Funky-Circuit/MOD1Bass/MOD1Bass_models/esp_lid.stl

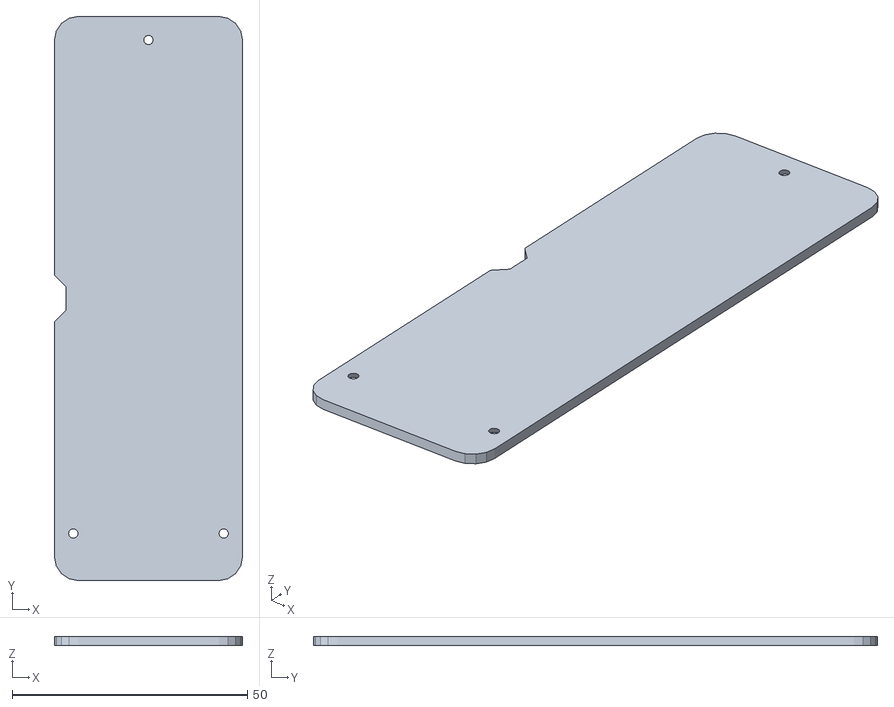
[picture p15: CAD file, 2026-07-26]
MOD1Bass_models/esp_lid.stl
40.0 x 120.0 x 2.00
