Funky-Circuit/MOD1Bass/MOD1Bass_models/body_right_b.stl

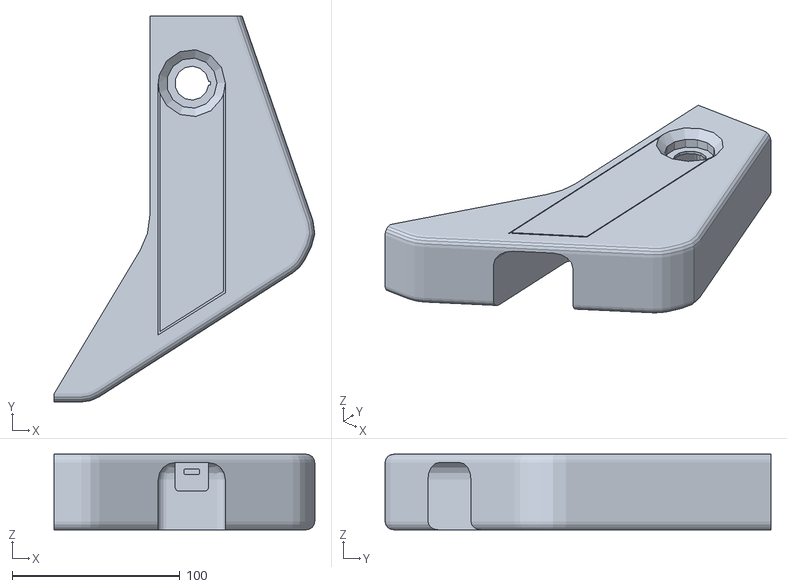
[picture p16: CAD file, 2026-07-26]
MOD1Bass_models/body_right_b.stl
155.3 x 230.0 x 45.0
