Funky-Circuit/MOD1Bass/MOD1Bass_models/body_left_b.stl

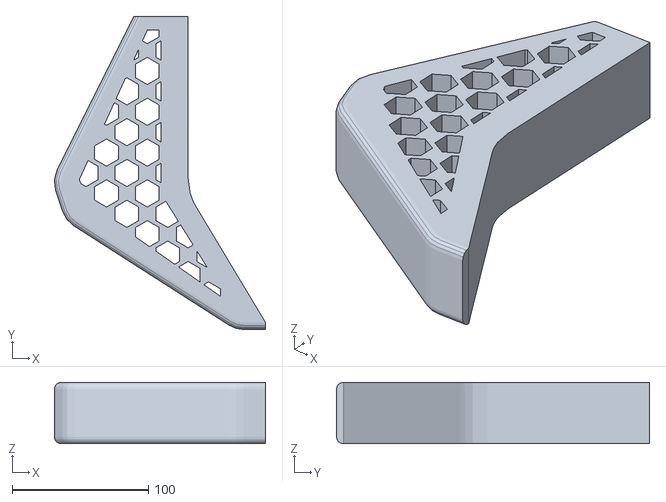
[picture p17: CAD file, 2026-07-26]
MOD1Bass_models/body_left_b.stl
155.4 x 230.0 x 45.0
