Funky-Circuit/MOD1Bass/MOD1Bass_models/neck_link.stl

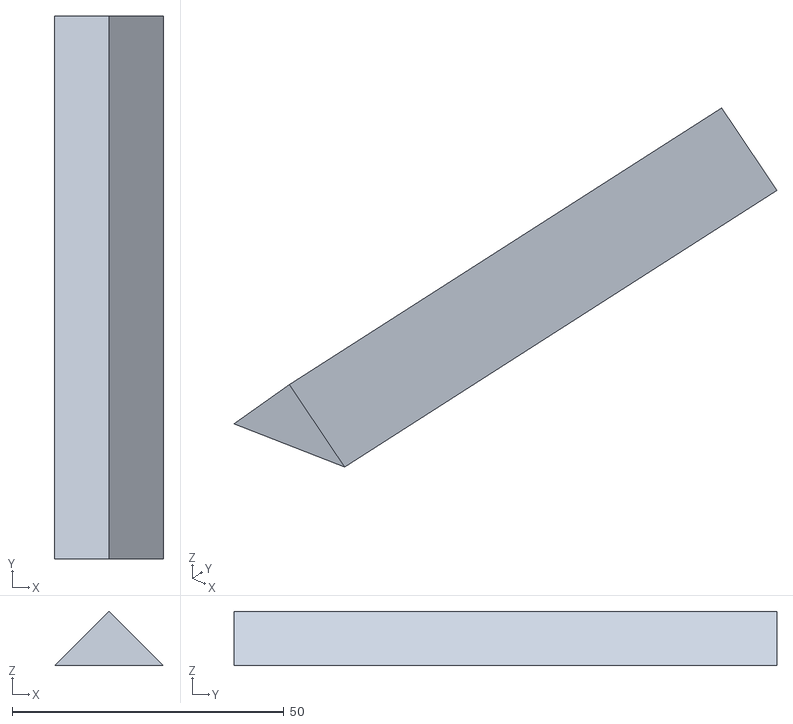
[picture p18: CAD file, 2026-07-26]
MOD1Bass_models/neck_link.stl
20.0 x 100.0 x 10.0
