Funky-Circuit/MOD1Bass/MOD1Bass_models/pcb_fsr_lid.stl

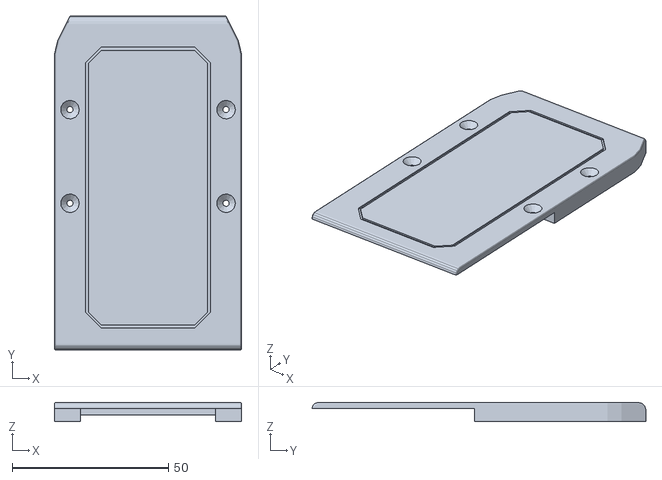
[picture p19: CAD file, 2026-07-26]
MOD1Bass_models/pcb_fsr_lid.stl
60.0 x 107.0 x 6.10
