Funky-Circuit/MOD1Bass/MOD1Bass_models/head_topper.stl

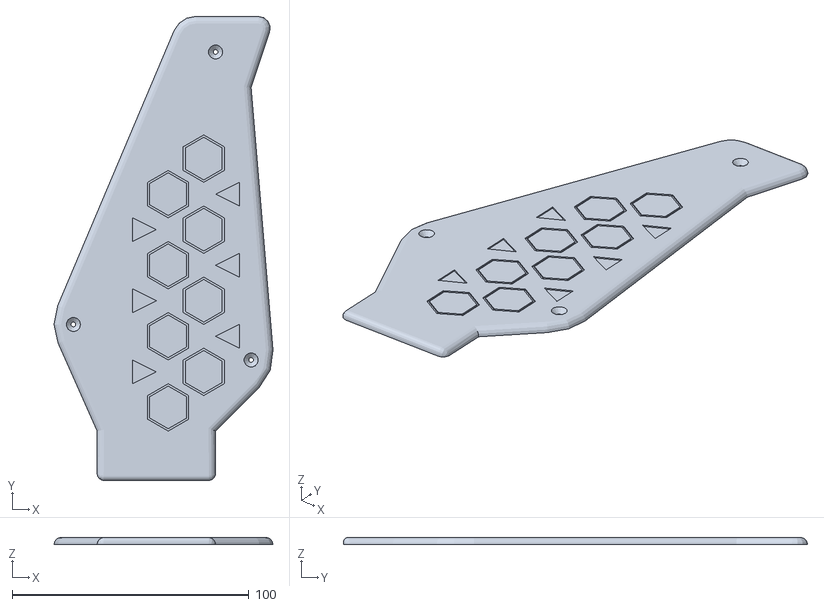
[picture p20: CAD file, 2026-07-26]
MOD1Bass_models/head_topper.stl
92.4 x 195.9 x 3.00
