Funky-Circuit/MOD1Bass/MOD1Bass_models/head.stl

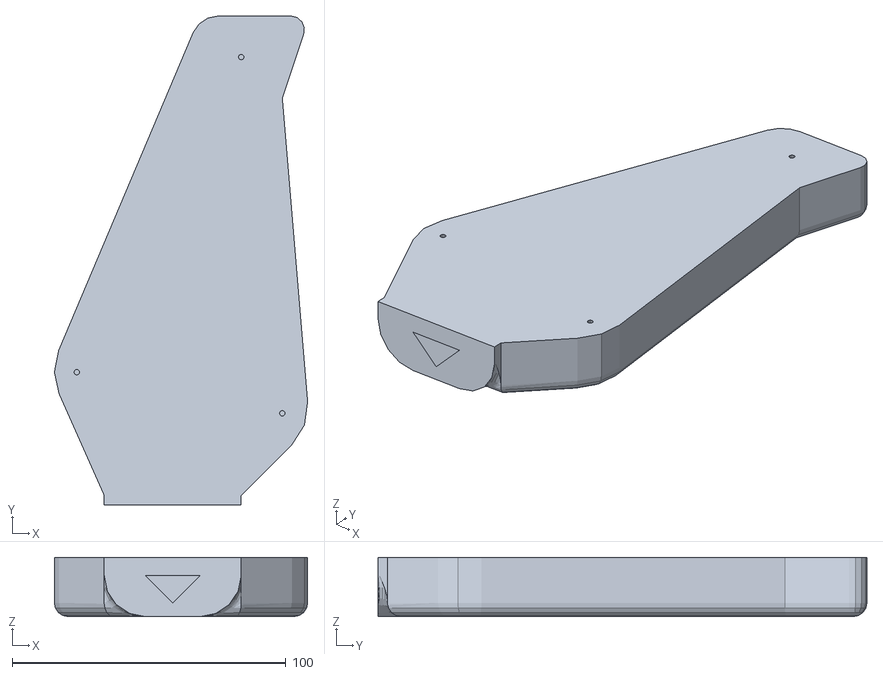
[picture p21: CAD file, 2026-07-26]
MOD1Bass_models/head.stl
92.4 x 178.5 x 21.6
